mcqn/my-babys-got-led/MGBLED-Detail-ESP.jpg

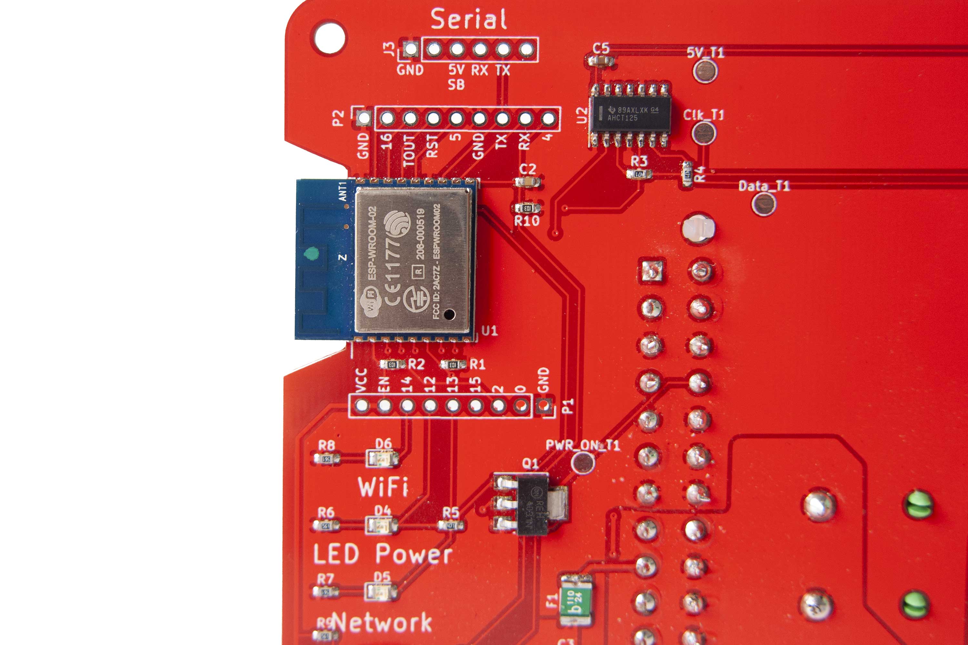
MGBLED-Detail-ESP.jpg
